Artilect-FabTronic/De-Electronique/Images/dessin_1x_de_en_perspective.png

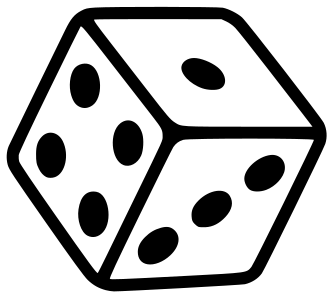
Images/dessin_1x_de_en_perspective.png
