Artilect-FabTronic/De-Electronique/Images/dessin_de.png

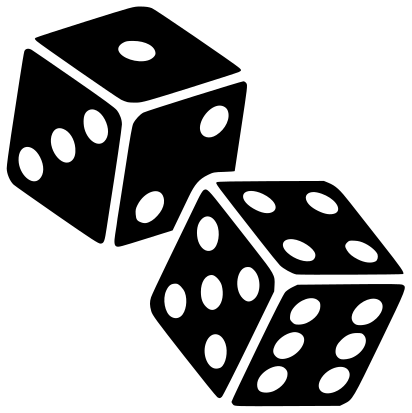
Images/dessin_de.png
