Artilect-FabTronic/De-Electronique/Images/led.png

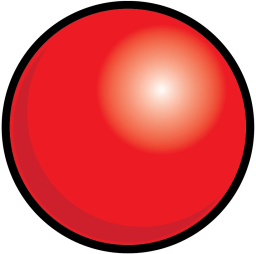
Images/led.png
