Artilect-FabTronic/De-Electronique/Images/vue_dessus.jpg

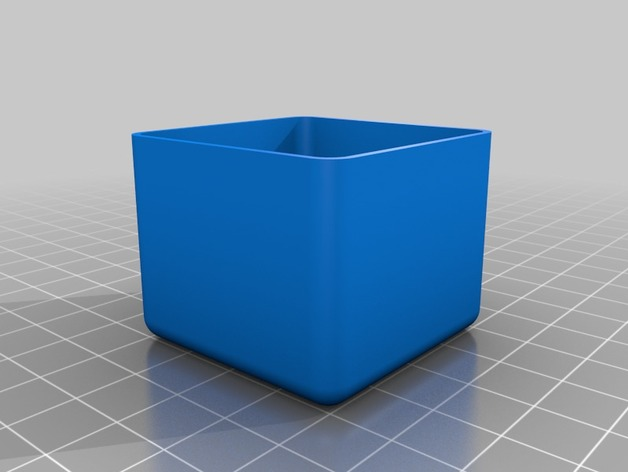
Images/vue_dessus.jpg
