Artilect-FabTronic/De-Electronique/Images/vue_ensemble_fonctionnel.jpg

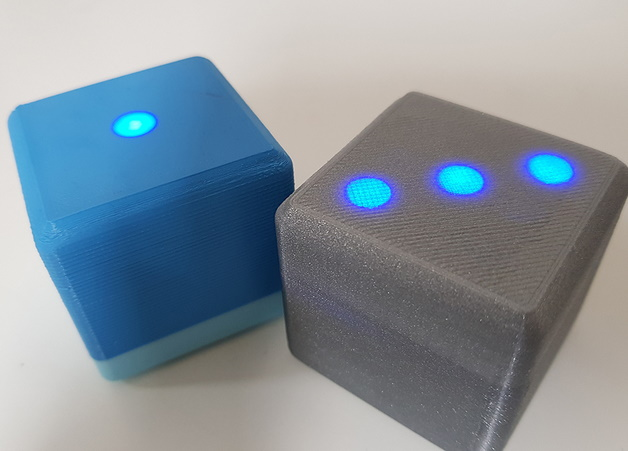
Images/vue_ensemble_fonctionnel.jpg
