Artilect-FabTronic/De-Electronique/Images/vue_assemblage_1.jpg

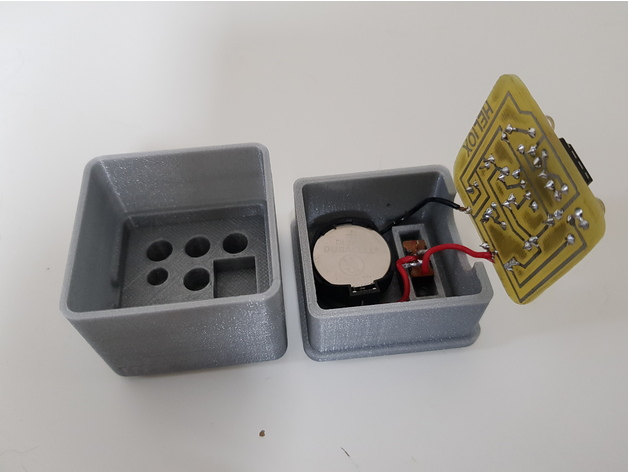
Images/vue_assemblage_1.jpg
