Artilect-FabTronic/De-Electronique/Images/vue_assemblage_2.jpg

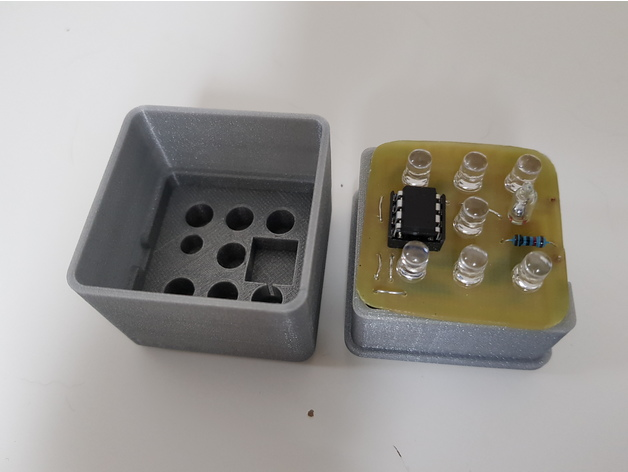
Images/vue_assemblage_2.jpg
