Artilect-FabTronic/De-Electronique/Images/vue_assemblage_3.jpg

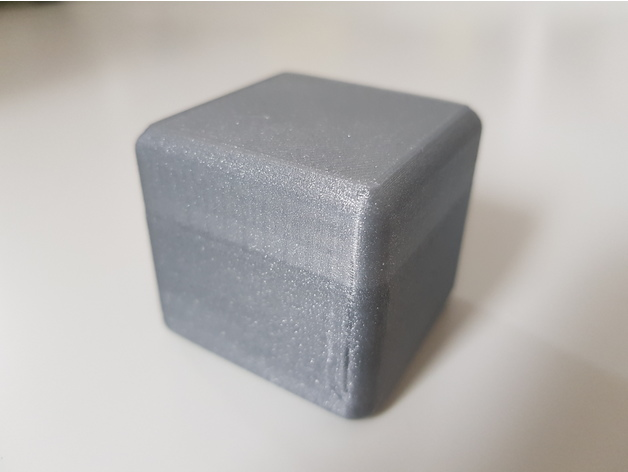
Images/vue_assemblage_3.jpg
